ElectronicCats/Escornabot-Makech/Makech/firmware/Escornabot/MoveList.h

// MoveList.h
/*

Copyright (C) 2014-2019 Escornabot - http://escornabot.com

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
See LICENSE.txt for details

*/

#ifndef _MOVE_LIST_H
#define _MOVE_LIST_H

#include <stdint.h>

#include "Configuration.h"
#include "Enums.h"

const static MOVE PROGRAM_ESCORNA_GREETING[] = {
    MOVE_FORWARD,
    MOVE_PAUSE,
    MOVE_LEFT,
    MOVE_PAUSE,
    MOVE_RIGHT,
    MOVE_RIGHT,
    MOVE_PAUSE,
    MOVE_LEFT,
    MOVE_BACKWARD,
    MOVE_NONE
};

/**
 * \brief Container of program movements.
 * \author @caligari
 */
class MoveList
{
public:

    /**
     * Constructor.
     */
    MoveList();

    /**
     * Removes all movements from program.
     */
    void clear();

    /**
     * Returns the amount of movements in program.
     * @return Amount of movements.
     */
    uint8_t getMoveCount();

    /**
     * Adds a new movement at the end of the program.
     * @param move The movement to add.
     */
    void addMove(MOVE move);

    /**
     * Adds a list of moves.
     */
    void addProgram(const MOVE moves[]);

    /**
     * Gets the movement from program at specified position.
     * @param index Position index (zero-based).
     */
    MOVE getMove(uint8_t index);

    /**
     * Gets the degrees to use with MOVE_LEFT or MOVE_RIGHT
     */
    uint16_t getTurnDegrees() { return _degrees; }

    /**
     * Sets the degrees to use with MOVE_LEFT or MOVE_RIGHT
     * @param degrees The degrees to turn left or right.
     */
    void setTurnDegrees(int16_t degrees) { _degrees = degrees; }

    /**
     * Gets the degrees to use with MOVE_ALT_LEFT or MOVE_ALT_RIGHT
     */
    uint16_t getAltTurnDegrees() { return _alt_degrees; }

    /**
     * Sets the degrees to use with MOVE_ALT_LEFT or MOVE_ALT_RIGHT
     * @param degrees The degrees to turn left or right.
     */
    void setAltTurnDegrees(int16_t degrees) { _alt_degrees = degrees; }


    #if USE_PERSISTENT_MEMORY

    /**
     * Saves the program in EEPROM.
     */
    void save();

    /**
     * Loads the program from EEPROM.
     */
    void load();

    #endif

private:

    uint8_t _move_count;

    MOVE _move_list[MOVE_LIMIT];

    int16_t _degrees;
    int16_t _alt_degrees;
};


#endif // _MOVE_LIST_H

// EOF
