ElectronicCats/Escornabot-Makech/Makech/firmware/Escornabot/Escornabot.h

// Escornabot.h
/*

Copyright (C) 2014-2019 Escornabot - http://escornabot.com

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
See LICENSE.txt for details

*/

#ifndef _ESCORNABOT_H
#define _ESCORNABOT_H

#define FIRMWARE_VERSION "v1.6.2"

#include <Arduino.h>
#include "Configuration.h"
#include "Enums.h"
#include "MoveList.h"
#include "Engine.h"
#include "ButtonSet.h"
#include "EventManager.h"

#if defined(ENGINE_TYPE_STEPPERS)

    #include "EngineSteppers.h"
    const EngineSteppers::Config ENGINE_CONFIG = {
        motor_left_in1: STEPPERS_MOTOR_LEFT_IN1,
        motor_left_in2: STEPPERS_MOTOR_LEFT_IN2,
        motor_left_in3: STEPPERS_MOTOR_LEFT_IN3,
        motor_left_in4: STEPPERS_MOTOR_LEFT_IN4,
        motor_right_in1: STEPPERS_MOTOR_RIGHT_IN1,
        motor_right_in2: STEPPERS_MOTOR_RIGHT_IN2,
        motor_right_in3: STEPPERS_MOTOR_RIGHT_IN3,
        motor_right_in4: STEPPERS_MOTOR_RIGHT_IN4,
        steps_per_second: STEPPERS_STEPS_PER_SECOND,
        line_steps: STEPPERS_LINE_STEPS,
        turn_steps: STEPPERS_TURN_STEPS,
    };
    EngineSteppers ENGINE_INSTANCE (&ENGINE_CONFIG);
    Engine* ENGINE = (Engine*) &ENGINE_INSTANCE;

#endif

#if defined(BUTTONS_DIGITAL)

    // digital button set
    #include "ButtonSetDigital.h"
    const ButtonSetDigital::Config BS_CONFIG = {
        pin_button_up: BS_DIGITAL_UP,
        pin_button_right: BS_DIGITAL_RIGHT,
        pin_button_down: BS_DIGITAL_DOWN,
        pin_button_left: BS_DIGITAL_LEFT,
        pin_button_go: BS_DIGITAL_GO,
        pin_button_reset: BS_DIGITAL_RESET,
    };
    ButtonSetDigital BUTTONS_INSTANCE (&BS_CONFIG);
    ButtonSet* BUTTONS = (ButtonSet*) &BUTTONS_INSTANCE;
    #define USE_BUTTONS true

#elif defined(BUTTONS_ANALOG)

    // analog button set
    #include "ButtonSetAnalog.h"
    const ButtonSetAnalog::Config BS_CONFIG = {
        pin_button_set: BS_ANALOG_PIN,
        pullup: (BS_ANALOG_WIRES == 3 ? false : true),
        value_button_up: BS_ANALOG_VALUE_UP,
        value_button_right: BS_ANALOG_VALUE_RIGHT,
        value_button_down: BS_ANALOG_VALUE_DOWN,
        value_button_left: BS_ANALOG_VALUE_LEFT,
        value_button_go: BS_ANALOG_VALUE_GO,
        value_button_reset: BS_ANALOG_VALUE_RESET,
    };
    ButtonSetAnalog BUTTONS_INSTANCE (&BS_CONFIG);
    ButtonSet* BUTTONS = (ButtonSet*) &BUTTONS_INSTANCE;
    #define USE_BUTTONS true

#endif // Button set

#if defined(USE_BLUETOOTH)

    #ifndef BLUETOOTH_SERIAL
        #define BLUETOOTH_SERIAL Serial
    #endif

    #include "BluetoothInterface.h"
    const BluetoothInterface::Config BT_CONFIG = {
        serial: &(BLUETOOTH_SERIAL),
        bauds: BLUETOOTH_BAUDS,
    };
    BluetoothInterface BLUETOOTH_INSTANCE (&BT_CONFIG);
    BluetoothInterface* BLUETOOTH = &BLUETOOTH_INSTANCE;

#endif // Bluetooth


#if USE_BUZZER
    #include "Buzzer.h"
    Buzzer BUZZER = Buzzer(BUZZER_PIN);
#endif


#if USE_SIMPLE_LED
    #include "SimpleLed.h"
    SimpleLed SIMPLE_LED = SimpleLed(SIMPLE_LED_PIN);
#endif


#if USE_KEYPAD_LEDS
    #include "KeypadLeds.h"
    const KeypadLeds::Config KEYPAD_LEDS_CONFIG = {
        pin_led_up: KEYPAD_LED_PIN_UP,
        pin_led_right: KEYPAD_LED_PIN_RIGHT,
        pin_led_down: KEYPAD_LED_PIN_DOWN,
        pin_led_left: KEYPAD_LED_PIN_LEFT,
        pin_led_go: KEYPAD_LED_PIN_GO,
    };
    KeypadLeds KEYPAD_LEDS = KeypadLeds(&KEYPAD_LEDS_CONFIG);
#endif

///// global vars

// event manager
EventManager EVENTS_INSTANCE;
EventManager* EVENTS = &EVENTS_INSTANCE;

// program
MoveList PROGRAM_INSTANCE;
MoveList* PROGRAM = &PROGRAM_INSTANCE;


#endif // _ESCORNABOT_H

// EOF
