ElectronicCats/Escornabot-Makech/Makech/firmware/Escornabot/BluetoothInterface.cpp

// BluetoothInterface.cpp
/*

Copyright (C) 2014-2019 Escornabot - http://escornabot.com

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
See LICENSE.txt for details

*/

#include "BluetoothInterface.h"
#include <string.h>

#define NL '\n'

//////////////////////////////////////////////////////////////////////

const static char* BUTTONS_PRESSED = "NESWGR";
const static char* BUTTONS_RELEASED = "neswgr";
const static char* SI_PROGRAM = "PRG:";

//////////////////////////////////////////////////////////////////////

#include "EventManager.h"
extern EventManager* EVENTS;

//////////////////////////////////////////////////////////////////////
//////////////////////////////////////////////////////////////////////

BluetoothInterface::BluetoothInterface(const Config* cfg)
{
    _config = cfg;
    _command_idx = 0;
}

//////////////////////////////////////////////////////////////////////
//////////////////////////////////////////////////////////////////////

void BluetoothInterface::init()
{
    ButtonSet::init();
    _config->serial->begin(_config->bauds, SERIAL_8N1);
}

//////////////////////////////////////////////////////////////////////
//////////////////////////////////////////////////////////////////////

void BluetoothInterface::scanButtons()
{
    while (_readLine())
    {
        // one-char commands
        char* found;
        if (strlen(_command) == 1)
        {
            found = strchr(BUTTONS_PRESSED, _command[0]);
            if (found)
            {
                BUTTON button = (BUTTON)((found - BUTTONS_PRESSED) + 1);
                EVENTS->indicateButtonLongReleased(button);
            }

            found = strchr(BUTTONS_RELEASED, _command[0]);
            if (found)
            {
                BUTTON button = (BUTTON)((found - BUTTONS_RELEASED) + 1);
                EVENTS->indicateButtonReleased(button);
            }
        }
        else if (strlen(_command) == 2 && _command[0] == _command[1])
        {
            found = strchr(BUTTONS_RELEASED, _command[0]);
            if (found)
            {
                BUTTON button = (BUTTON)((found - BUTTONS_RELEASED) + 1);
                EVENTS->indicateButtonLongReleased(button);
            }
        }
    }
}

//////////////////////////////////////////////////////////////////////
//////////////////////////////////////////////////////////////////////

bool BluetoothInterface::_readLine()
{
    while (_config->serial->available())
    {
        char key = _config->serial->read();

        if (key == NL)
        {
            _command[_command_idx] = '\0';
            _command_idx = 0;
            return true;
        }

        if (_command_idx < COMMAND_MAX_LENGTH)
        {
            _command[_command_idx++] = key;
        }
    }
    return false;
}

//////////////////////////////////////////////////////////////////////
//////////////////////////////////////////////////////////////////////

void BluetoothInterface::MoveExecuting(MOVE move)
{
    _config->serial->print(BUTTONS_PRESSED[move - 1]);
    _config->serial->print(NL);
}

//////////////////////////////////////////////////////////////////////
//////////////////////////////////////////////////////////////////////

void BluetoothInterface::MoveExecuted(MOVE move)
{
    _config->serial->print(BUTTONS_RELEASED[move - 1]);
    _config->serial->print(NL);
}

//////////////////////////////////////////////////////////////////////
//////////////////////////////////////////////////////////////////////

void BluetoothInterface::MoveAdded(MOVE move)
{
    _config->serial->print(SI_PROGRAM);
    _config->serial->print(move);
    _config->serial->print(' ');
    _config->serial->print(BUTTONS_RELEASED[move - 1]);
    _config->serial->print(NL);
}

//////////////////////////////////////////////////////////////////////
//////////////////////////////////////////////////////////////////////

void BluetoothInterface::ProgramStarted(uint8_t total_moves)
{
    _config->serial->print(SI_PROGRAM);
    _config->serial->print("GO ");
    _config->serial->print(total_moves);
    _config->serial->print(NL);
}

//////////////////////////////////////////////////////////////////////
//////////////////////////////////////////////////////////////////////

void BluetoothInterface::ProgramFinished()
{
    _config->serial->print(SI_PROGRAM);
    _config->serial->print("END");
    _config->serial->print(NL);
}

//////////////////////////////////////////////////////////////////////
//////////////////////////////////////////////////////////////////////

void BluetoothInterface::ProgramReset()
{
    _config->serial->print(SI_PROGRAM);
    _config->serial->print("RESET");
    _config->serial->print(NL);
}

//////////////////////////////////////////////////////////////////////
//////////////////////////////////////////////////////////////////////

void BluetoothInterface::ProgramAborted(uint8_t executed, uint8_t total)
{
    _config->serial->print(SI_PROGRAM);
    _config->serial->print("ABORTED ");
    _config->serial->print(executed);
    _config->serial->print("/");
    _config->serial->print(total);
    _config->serial->print(NL);
}

//////////////////////////////////////////////////////////////////////
//////////////////////////////////////////////////////////////////////


// EOF
