ElectronicCats/Escornabot-Makech/Makech/firmware/Escornabot/Bot.cpp

// Bot.cpp
/*

Copyright (C) 2014-2019 Escornabot - http://escornabot.com

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
See LICENSE.txt for details

*/

#include "Bot.h"
#include "Escornabot.h"

//////////////////////////////////////////////////////////////////////

void Bot::init()
{
    // init engine
    ENGINE->init();

    // init button set
    #if USE_BUTTONS
    BUTTONS->init();
    #endif

    // early console
    Serial.begin(9600);
    Serial.println(FIRMWARE_VERSION);
    delay(100);

    // init bluetooth
    #if USE_BLUETOOTH
    BLUETOOTH->init();
    #endif

    // init buzzer
    #if USE_BUZZER
    BUZZER.init();
    BUZZER.beep();
    #endif

    #if USE_SIMPLE_LED
    SIMPLE_LED.init();
    #endif

    #if USE_KEYPAD_LEDS
    KEYPAD_LEDS.init();
    #endif

    // restore last program
    #if USE_PERSISTENT_MEMORY
    PROGRAM->load();
    #endif

    EVENTS->add(this);
}

//////////////////////////////////////////////////////////////////////

void Bot::loop()
{
    EVENTS->indicateTick(micros());

    if (!ENGINE->isExecuting()) delay(10);
}

//////////////////////////////////////////////////////////////////////

void Bot::buttonPressed(BUTTON button)
{
    #if USE_SIMPLE_LED
    SIMPLE_LED.setStatus(true);
    #endif
}

//////////////////////////////////////////////////////////////////////

void Bot::buttonReleased(BUTTON button)
{
    #if USE_SIMPLE_LED
    SIMPLE_LED.setStatus(false);
    #endif

    if (ENGINE->isExecuting())
    {
        ENGINE->cancelExecution();
        return;
    }

    switch (button)
    {
        case BUTTON_UP:
            _storeMove(MOVE_FORWARD);
            break;

        case BUTTON_RIGHT:
            _storeMove(MOVE_RIGHT);
            break;

        case BUTTON_DOWN:
            _storeMove(MOVE_BACKWARD);
            break;

        case BUTTON_LEFT:
            _storeMove(MOVE_LEFT);
            break;

        case BUTTON_GO:
            _go();
            break;

        case BUTTON_RESET:
            PROGRAM->clear();
            break;
    }
}

//////////////////////////////////////////////////////////////////////

void Bot::buttonLongReleased(BUTTON button)
{
    #if USE_SIMPLE_LED
    SIMPLE_LED.setStatus(false);
    #endif

    if (ENGINE->isExecuting())
    {
        ENGINE->cancelExecution();
        return;
    }

    switch (button)
    {
        case BUTTON_RIGHT:
            _storeMove(MOVE_ALT_RIGHT);
            break;

        case BUTTON_DOWN:
            _storeMove(MOVE_PAUSE);
            break;

        case BUTTON_LEFT:
            _storeMove(MOVE_ALT_LEFT);
            break;

        case BUTTON_GO:
            _next_game_mode();
            break;
    }
}

//////////////////////////////////////////////////////////////////////

void Bot::programFinished()
{
    #if PROGRAM_RESET_ALWAYS
    PROGRAM->clear();
    #endif

    #if USE_BUZZER
    BUZZER.playRttl(PROGRAM_FINISHED_RTTL);
    #endif

    if (_game_mode == GAME_MODE_GRID_90 && !ENGINE->isAligned(90))
    {
        // advise next advance is expected to be a diagonal:
        #if USE_SIMPLE_LED
        SIMPLE_LED.setStatus(true);
        #elif USE_KEYPAD_LEDS
        KEYPAD_LEDS.setLed(BUTTON_RIGHT, true);
        KEYPAD_LEDS.setLed(BUTTON_LEFT, true);
        #endif
    }
}

//////////////////////////////////////////////////////////////////////

void Bot::programAborted(uint8_t executed, uint8_t total)
{
    #if PROGRAM_RESET_ALWAYS
    PROGRAM->clear();
    #endif
}

//////////////////////////////////////////////////////////////////////

void Bot::_go()
{
    // preloaded program
    if (PROGRAM->getMoveCount() == 0 && _total_programs == 0)
    {
        PROGRAM->addProgram(PROGRAM_ESCORNA_GREETING);
    }

    // only with movements
    if (PROGRAM->getMoveCount() > 0)
    {
        #if USE_PERSISTENT_MEMORY
        // save the movement program in EEPROM
        PROGRAM->save();
        #endif

        // let user to release the 'go' button before the action
        delay(DELAY_BEFORE_GO);

        ENGINE->execute(PROGRAM, AFTER_MOVEMENT_PAUSE, POV_ESCORNABOT);
        _total_programs++;
    }
}

//////////////////////////////////////////////////////////////////////

void Bot::_storeMove(MOVE move)
{
    if (PROGRAM->getMoveCount() < MOVE_LIMIT)
    {
        PROGRAM->addMove(move);
    }
    else
    {
        // memory is full
        _go();
    }
}

//////////////////////////////////////////////////////////////////////

void Bot::_next_game_mode()
{
    // select the next game mode (2 modes currently available)
    ++_game_mode %= 2;

    switch (_game_mode)
    {
        case GAME_MODE_GRID_90:
            PROGRAM->setTurnDegrees(90);
            PROGRAM->setAltTurnDegrees(45);
            ENGINE->setSquareDiagonals(true);
            break;

        case GAME_MODE_GRID_60:
            PROGRAM->setTurnDegrees(60);
            PROGRAM->setAltTurnDegrees(120);
            ENGINE->setSquareDiagonals(false);
            break;
    }

    EVENTS->indicateGameModeSelected(_game_mode);
}

//////////////////////////////////////////////////////////////////////

// EOF
