ElectronicCats/Escornabot-Makech/Makech/firmware/Escornabot/Buzzer.h

// Buzzer.h
/*

Copyright (C) 2014-2019 Escornabot - http://escornabot.com

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
See LICENSE.txt for details

*/

#ifndef _BUZZER_H
#define _BUZZER_H

#define RTTL_INTEL ":d=16,o=5,b=320:d,p,d,p,d,p,g,p,g,p,g,p,d,p,d,p,d,p,a,p,a,p,"
#define RTTL_FIDO ":d=16,o=6,b=800:f,4p,f,4p,f,4p,f,4p,c,4p,c,4p,c,4p,c,"
#define RTTL_MOSAIC ":d=8,o=6,b=400:c,e,g,e,c,g,e,g,c,g,c,e,c,g,e,g,e,c,"
#define RTTL_ELISA ":d=4,o=7,b=125:e,d#,e,d#,e,b#,d,c,8a,"

#define BUZZER_BEEP_FREQUENCY 4699
#define BUZZER_BEEP_MILLIS 100

#include <stdint.h>
#include "EventListener.h"

/**
 * \brief Generates tones with a buzzer connected to a PWM output.
 * \author @caligari
 */
class Buzzer : public EventListener
{
public:

    /**
     * Constructor.
     * @param pin Pin where the buzzer is connected (PWM output)
     */
    Buzzer(uint8_t pin);

    /**
     * Does the hardware initialization.
     */
    void init();

    /**
     * Simple beep generator.
     */
    void beep() { beep(BUZZER_BEEP_FREQUENCY); }

    /**
     * Beep generator with a tone.
     */
    void beep(uint16_t frequency);

    /**
     * RTTL parser and tone player.
     * @param rttl Ring Tone Transfer Language string.
     */
    void playRttl(const char* rttl);


    //////////////////////////////////////////////////////////////////////
    // Buzzer interface
    //////////////////////////////////////////////////////////////////////

    virtual void buttonReleased(BUTTON btn)
        { _beepDirection(btn, BUZZER_BEEP_MILLIS); }

    virtual void buttonLongReleased(BUTTON btn)
        { _beepDirection(btn, 2 * BUZZER_BEEP_MILLIS); }

    virtual void moveExecuting(MOVE move)
        { _beepDirection(move, BUZZER_BEEP_MILLIS); }

    virtual void gameModeSelected(GAME_MODE mode);

private:

    uint8_t _pin;

    void _beepDirection(uint8_t direction, uint16_t duration);

};

#endif // _BUZZER_H

// EOF
