ElectronicCats/Escornabot-Makech/Makech/firmware/Escornabot/PersistentMemory.h

// PersistentMemory.h
/*

Copyright (C) 2014-2019 Escornabot - http://escornabot.com

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
See LICENSE.txt for details

*/

#ifndef _PERSISTENT_MEMORY_H
#define _PERSISTENT_MEMORY_H

#include <stddef.h>
#include <stdint.h>
#include "Enums.h"
#include "MoveList.h"

// eeprom organization
#define EEPROM_ADDR_MOVE_LIST 0
#define EEPROM_SIZE_MOVE_LIST (MOVE_LIMIT + 1)

/**
 * \brief Provides convenient methods to use persistent memory (EEPROM).
 * \author @caligari
 */
class PersistentMemory
{
public:

    /**
     * Saves the list of movements in EEPROM.
     * @param move_list Array with the movements.
     * @param move_count Number of movements.
     * @return OK is true. Error is false.
     */
    bool saveProgram(MOVE* move_list, uint8_t move_count);

    /**
     * Loads a program of movements from EEPROM.
     * @param move_list Array with the movements.
     * @param move_count Number of movements.
     * @return OK is true. Error is false.
     */
    bool loadProgram(MOVE* move_list, uint8_t *move_count);

private:

    /**
     * Returns the size of persistent memory.
     *
     * @return Amount of memory in bytes.
     */
    size_t _totalBytes();

    /**
     * Saves a buffer to the persistent memory.
     *
     * @address Persistent memory address.
     * @buffer Main memory pointer with the data to save.
     * @size Length in bytes of the buffer to save.
     */
    bool _save(size_t address, uint8_t* buffer, size_t length);

    /**
     * Loads a buffer from the persistent memory.
     *
     * @address Persistent memory address.
     * @buffer Main memory pointer where the data will be loaded.
     * @size Length in bytes of the buffer to load.
     * @return OK is true. Error is false.
     */
    bool _load(size_t address, uint8_t* buffer, size_t length);

    /**
     * Fills the memory with zeroes.
     */
    void _clear();

};


#endif // _PERSISTENT_MEMORY_H

// EOF
