ElectronicCats/Escornabot-Makech/Makech/firmware/bootloader_uf2_makech/update-bootloader-escornabot_makech-v3.3.0-60-gd8dcad0-dirty.ino

// Bootloader update sketch. Paste into Arduino IDE and upload to the device
// to update bootloader. It will blink a few times and then start pulsing.
// Your OS will then detect a USB mass storage device.
#include <stdint.h>
const uint8_t bootloader[8192] __attribute__ ((aligned (4))) = {0xd8, 0x2d, 0x00, 0x20, 0x89, 0x02, 0x00, 0x00, 0x85, 0x02, 0x00, 0x00, 0x87, 0x02, 0x00, 0x00,
0x00, 0x00, 0x00, 0x00, 0x00, 0x00, 0x00, 0x00, 0x00, 0x00, 0x00, 0x00, 0x00, 0x00, 0x00, 0x00,
0x00, 0x00, 0x00, 0x00, 0x00, 0x00, 0x00, 0x00, 0x00, 0x00, 0x00, 0x00, 0x85, 0x02, 0x00, 0x00,
0x00, 0x00, 0x00, 0x00, 0x00, 0x00, 0x00, 0x00, 0x85, 0x02, 0x00, 0x00, 0x7d, 0x02, 0x00, 0x00,
0x85, 0x02, 0x00, 0x00, 0x85, 0x02, 0x00, 0x00, 0x85, 0x02, 0x00, 0x00, 0x85, 0x02, 0x00, 0x00,
0x85, 0x02, 0x00, 0x00, 0x85, 0x02, 0x00, 0x00, 0x85, 0x02, 0x00, 0x00, 0x85, 0x02, 0x00, 0x00,
0x85, 0x02, 0x00, 0x00, 0x85, 0x02, 0x00, 0x00, 0x85, 0x02, 0x00, 0x00, 0x85, 0x02, 0x00, 0x00,
0x85, 0x02, 0x00, 0x00, 0x85, 0x02, 0x00, 0x00, 0x85, 0x02, 0x00, 0x00, 0x85, 0x02, 0x00, 0x00,
0x85, 0x02, 0x00, 0x00, 0x85, 0x02, 0x00, 0x00, 0x85, 0x02, 0x00, 0x00, 0x85, 0x02, 0x00, 0x00,
0x85, 0x02, 0x00, 0x00, 0x00, 0x00, 0x00, 0x00, 0x00, 0x00, 0x00, 0x00, 0x85, 0x02, 0x00, 0x00,
0x85, 0x02, 0x00, 0x00, 0x85, 0x02, 0x00, 0x00, 0x85, 0x02, 0x00, 0x00, 0x85, 0x02, 0x00, 0x00,
0x00, 0x00, 0x00, 0x00, 0x07, 0x4b, 0x1a, 0x00, 0x19, 0x7d, 0xc9, 0x07, 0xfc, 0xd5, 0x20, 0x21,
0xff, 0x31, 0x19, 0x83, 0x04, 0x49, 0x40, 0x08, 0xd8, 0x61, 0x19, 0x80, 0x13, 0x7d, 0xdb, 0x07,
0xfc, 0xd5, 0x70, 0x47, 0x00, 0x40, 0x00, 0x41, 0x02, 0xa5, 0xff, 0xff, 0x10, 0xb5, 0x04, 0x00,
0x04, 0x4b, 0x9c, 0x42, 0x00, 0xd9, 0x10, 0xbd, 0x20, 0x00, 0x01, 0x34, 0xff, 0xf7, 0xe2, 0xff,
0xff, 0x34, 0xf5, 0xe7, 0xff, 0xff, 0x03, 0x00, 0x00, 0x23, 0x30, 0xb5, 0x9a, 0x42, 0x00, 0xd1,
0x30, 0xbd, 0x9c, 0x00, 0x0d, 0x59, 0x01, 0x33, 0x05, 0x51, 0xf7, 0xe7, 0xf0, 0xb5, 0x80, 0x25,
0x10, 0x4b, 0x11, 0x4e, 0x5c, 0x68, 0x11, 0x4f, 0xac, 0x43, 0x5c, 0x60, 0x00, 0x2a, 0x00, 0xd1,
0xf0, 0xbd, 0x14, 0x00, 0x10, 0x2a, 0x00, 0xd9, 0x10, 0x24, 0x12, 0x1b, 0x1e, 0x80, 0x1d, 0x7d,
0xed, 0x07, 0xfc, 0xd5, 0xa4, 0x00, 0xa4, 0x46, 0x00, 0x24, 0x0d, 0x59, 0x05, 0x51, 0x04, 0x34,
0x64, 0x45, 0xfa, 0xd1, 0x00, 0x19, 0x09, 0x19, 0x1f, 0x80, 0x1c, 0x7d, 0xe4, 0x07, 0xfc, 0xd5,
0xe4, 0xe7, 0xc0, 0x46, 0x00, 0x40, 0x00, 0x41, 0x44, 0xa5, 0xff, 0xff, 0x04, 0xa5, 0xff, 0xff,
0x80, 0x22, 0x70, 0xb5, 0x00, 0x23, 0x04, 0x00, 0x0d, 0x00, 0x52, 0x00, 0xe9, 0x58, 0xe0, 0x58,
0x81, 0x42, 0x03, 0xd1, 0x04, 0x33, 0x93, 0x42, 0xf8, 0xd1, 0x70, 0xbd, 0x20, 0x00, 0xff, 0xf7,
0x99, 0xff, 0x40, 0x22, 0x29, 0x00, 0x20, 0x00, 0xff, 0xf7, 0xc0, 0xff, 0xf5, 0xe7, 0x00, 0x00,
0x02, 0x4a, 0x53, 0x78, 0x5b, 0xb2, 0x00, 0x2b, 0xfb, 0xdb, 0x70, 0x47, 0x00, 0x0c, 0x00, 0x40,
0x10, 0x23, 0x02, 0x49, 0xca, 0x68, 0x1a, 0x42, 0xfc, 0xd0, 0x70, 0x47, 0x00, 0x08, 0x00, 0x40,
0x1e, 0x21, 0xf8, 0xb5, 0x02, 0x26, 0x25, 0x4a, 0x25, 0x4c, 0x53, 0x68, 0x25, 0x4d, 0x8b, 0x43,
0x33, 0x43, 0x53, 0x60, 0xa6, 0x60, 0xff, 0xf7, 0xe3, 0xff, 0x23, 0x4b, 0x63, 0x60, 0xff, 0xf7,
0xdf, 0xff, 0xae, 0x84, 0xff, 0xf7, 0xe4, 0xff, 0x20, 0x4b, 0x1b, 0x68, 0x9b, 0x0e, 0x3f, 0x2b,
0x00, 0xd1, 0x20, 0x3b, 0x00, 0x26, 0x02, 0x27, 0x1d, 0x4a, 0x9b, 0x02, 0x13, 0x43, 0x1d, 0x4a,
0xea, 0x62, 0xab, 0x62, 0xae, 0x84, 0xff, 0xf7, 0xd3, 0xff, 0x1b, 0x4b, 0xab, 0x84, 0xff, 0xf7,
0xcf, 0xff, 0xab, 0x8c, 0x3b, 0x43, 0xab, 0x84, 0xff, 0xf7, 0xca, 0xff, 0x3f, 0x22, 0x63, 0x88,
0x93, 0x43, 0x80, 0x22, 0x1f, 0x43, 0x67, 0x80, 0x63, 0x88, 0xd2, 0x01, 0x13, 0x43, 0x63, 0x80,
0xa6, 0x60, 0xff, 0xf7, 0xb5, 0xff, 0x11, 0x4b, 0x63, 0x60, 0xff, 0xf7, 0xb1, 0xff, 0xc0, 0x21,
0x0f, 0x4a, 0x10, 0x4b, 0x10, 0x48, 0x53, 0x60, 0x03, 0x6a, 0x09, 0x06, 0x1b, 0x02, 0x1b, 0x0a,
0x0b, 0x43, 0x03, 0x62, 0x07, 0x23, 0x96, 0x60, 0x13, 0x60, 0xf8, 0xbd, 0x00, 0x40, 0x00, 0x41,
0x00, 0x0c, 0x00, 0x40, 0x00, 0x08, 0x00, 0x40, 0x06, 0x00, 0x01, 0x00, 0x24, 0x60, 0x80, 0x00,
0xff, 0x01, 0x00, 0x00, 0x80, 0xbb, 0x0a, 0x1c, 0x24, 0x05, 0x00, 0x00, 0x00, 0x07, 0x03, 0x00,
0x10, 0xe0, 0x00, 0xe0, 0xe7, 0x03, 0x00, 0x00, 0x00, 0xed, 0x00, 0xe0, 0x10, 0xb5, 0x00, 0xf0,
0xf1, 0xf8, 0x10, 0xbd, 0xfe, 0xe7, 0xfe, 0xe7, 0x20, 0x48, 0x21, 0x49, 0x70, 0xb5, 0x00, 0x23,
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

};
const uint16_t bootloader_crcs[] = {0x417d ,0xc21a ,0x83d5 ,0xcde6 ,0xe0dd ,0x6c7a ,0xaee4 ,0x694c};
#define BOOTLOADER_K 8

static uint16_t crcCache[256];

#define CRC16POLY 0x1021

#define FLASH_ROW_SIZE (FLASH_PAGE_SIZE * 4)

uint16_t add_crc(uint8_t ch, unsigned short crc0) {
    if (!crcCache[1]) {
        for (int ptr = 0; ptr < 256; ptr++) {
            uint16_t crc = (int)ptr << 8;
            for (uint16_t cmpt = 0; cmpt < 8; cmpt++) {
                if (crc & 0x8000)
                    crc = crc << 1 ^ CRC16POLY;
                else
                    crc = crc << 1;
            }
            crcCache[ptr] = crc;
        }
    }

    return ((crc0 << 8) ^ crcCache[((crc0 >> 8) ^ ch) & 0xff]) & 0xffff;
}

uint8_t pageBuf[FLASH_ROW_SIZE];

#define NVM_USER_MEMORY ((volatile uint16_t *)NVMCTRL_USER)

static inline void wait_ready(void) {
    while (NVMCTRL->INTFLAG.bit.READY == 0) {
    }
}

void flash_erase_row(uint32_t *dst) {
    wait_ready();
    NVMCTRL->STATUS.reg = NVMCTRL_STATUS_MASK;

    // Execute "ER" Erase Row
    NVMCTRL->ADDR.reg = (uint32_t)dst / 2;
    NVMCTRL->CTRLA.reg = NVMCTRL_CTRLA_CMDEX_KEY | NVMCTRL_CTRLA_CMD_ER;
    wait_ready();
}

void flash_write_words(uint32_t *dst, uint32_t *src, uint32_t n_words) {
    // Set automatic page write
    NVMCTRL->CTRLB.bit.MANW = 0;

    while (n_words > 0) {
        uint32_t len = min(FLASH_PAGE_SIZE >> 2, n_words);
        n_words -= len;

        // Execute "PBC" Page Buffer Clear
        NVMCTRL->CTRLA.reg = NVMCTRL_CTRLA_CMDEX_KEY | NVMCTRL_CTRLA_CMD_PBC;
        wait_ready();

        // make sure there are no other memory writes here
        // otherwise we get lock-ups

        while (len--)
            *dst++ = *src++;

        // Execute "WP" Write Page
        NVMCTRL->CTRLA.reg = NVMCTRL_CTRLA_CMDEX_KEY | NVMCTRL_CTRLA_CMD_WP;
        wait_ready();
    }
}

void flash_write_row(uint32_t *dst, uint32_t *src) {
    flash_erase_row(dst);
    flash_write_words(dst, src, FLASH_ROW_SIZE / 4);
}

#define exec_cmd(cmd)                                                                              \
    do {                                                                                           \
        NVMCTRL->STATUS.reg |= NVMCTRL_STATUS_MASK;                                                \
        NVMCTRL->ADDR.reg = (uint32_t)NVMCTRL_USER / 2;                                            \
        NVMCTRL->CTRLA.reg = NVMCTRL_CTRLA_CMDEX_KEY | cmd;                                        \
        while (NVMCTRL->INTFLAG.bit.READY == 0)                                                    \
            ;                                                                                      \
    } while (0)

void setBootProt(int v) {
    uint32_t fuses[2];

    while (!(NVMCTRL->INTFLAG.reg & NVMCTRL_INTFLAG_READY))
        ;

    fuses[0] = *((uint32_t *)NVMCTRL_AUX0_ADDRESS);
    fuses[1] = *(((uint32_t *)NVMCTRL_AUX0_ADDRESS) + 1);

    uint32_t bootprot = (fuses[0] & NVMCTRL_FUSES_BOOTPROT_Msk) >> NVMCTRL_FUSES_BOOTPROT_Pos;

    if (bootprot == v)
        return;

    fuses[0] = (fuses[0] & ~NVMCTRL_FUSES_BOOTPROT_Msk) | (v << NVMCTRL_FUSES_BOOTPROT_Pos);

    NVMCTRL->CTRLB.reg = NVMCTRL->CTRLB.reg | NVMCTRL_CTRLB_CACHEDIS | NVMCTRL_CTRLB_MANW;

    exec_cmd(NVMCTRL_CTRLA_CMD_EAR);
    exec_cmd(NVMCTRL_CTRLA_CMD_PBC);

    *((uint32_t *)NVMCTRL_AUX0_ADDRESS) = fuses[0];
    *(((uint32_t *)NVMCTRL_AUX0_ADDRESS) + 1) = fuses[1];

    exec_cmd(NVMCTRL_CTRLA_CMD_WAP);

    NVIC_SystemReset();
}

void mydelay(int ms) {
    ms <<= 13;
    while (ms--) {
        asm("nop");
    }
}

void setup() {
    pinMode(LED_BUILTIN, OUTPUT);
    digitalWrite(LED_BUILTIN, HIGH);

    if (8 << NVMCTRL->PARAM.bit.PSZ != FLASH_PAGE_SIZE)
        while (1) {
        }

    __disable_irq();

    setBootProt(7); // 0k

    const uint8_t *ptr = bootloader;
    int i;

    for (i = 0; i < BOOTLOADER_K; ++i) {
        int crc = 0;
        for (int j = 0; j < 1024; ++j) {
            crc = add_crc(*ptr++, crc);
        }
        if (bootloader_crcs[i] != crc) {
            while (1) {
            }
        }
    }

    for (i = 0; i < BOOTLOADER_K * 1024; i += FLASH_ROW_SIZE) {
        memcpy(pageBuf, &bootloader[i], FLASH_ROW_SIZE);
        flash_write_row((uint32_t *)(void *)i, (uint32_t *)(void *)pageBuf);
    }

    // re-base int vector back to bootloader, so that the flash erase below doesn't write over the
    // vectors
    SCB->VTOR = 0;

    // erase first row of this updater app, so the bootloader doesn't start us again
    flash_erase_row((uint32_t *)(void *)(BOOTLOADER_K * 1024));

    for (i = 0; i < 5; ++i) {
        digitalWrite(LED_BUILTIN, HIGH);
        mydelay(100);
        digitalWrite(LED_BUILTIN, LOW);
        mydelay(200);
    }

    setBootProt(2); // 8k

    while (1) {
    }
}

void loop() {}
